LouiseLeciak/Module-elec-LilyPad/firmware/src/app/game.c

#include "app/game.h"

#include "app/menu.h"
#include "display/GC9A01.h"
#include "display/ili9488.h"
#include "display/screen_text.h"
#include "input/keypad.h"
#include "storage/fatfs.h"
#include "storage/sd_streaming.h"
#include "system/globals.h"
#include "system/power_save.h"
#include "system/uart.h"
#include "utils/utils.h"

uint8_t game_choice = 0;
game_state_t game_state = GAME_MENU;
char game_target;
// the different choices you have
char game_answers[GAME_CHOICES];
uint8_t game_answer = 0;  // player answer
uint32_t random_state = 0;

static const char game_characters[] = "0123456789ABCDEFGHIJKLMNOPQRSTUVWXYZ";

// manage keyboard in game mdd
void game()
{
  int key = keypad_read();

  if (key >= 0)
  {
    if (inac == 1)
    {
      power_save_activity();
      return;
    }
    else
      power_save_activity();
    uint8_t row = key / COLS_NB;
    uint8_t col = key % COLS_NB;
    char c = keymap[row][col];

    if (c == HOME)
    {
      show_menu();
    }

    _delay_ms(20);

    while (keypad_read() >= 0)
    {
      ;
    }
  }
}

// display teh game menu
void show_game(void)
{
  ili9488_fill_screen(GC9A01A_COLOR_OLIVE);
  if (language == LANG_FR)
  {
    draw_string(125, 20, "JEU", GC9A01A_COLOR_GREEN, GC9A01A_COLOR_OLIVE, 4, 2);

    draw_string(10, 120, "> ", GC9A01A_COLOR_GREEN, GC9A01A_COLOR_OLIVE, 4, 2);

    draw_string(70, 120, "Lettre", GC9A01A_COLOR_GREEN, GC9A01A_COLOR_OLIVE, 4,
                2);

    draw_string(70, 220, "Signe", GC9A01A_COLOR_GREEN, GC9A01A_COLOR_OLIVE, 4,
                2);
  }
  else if (language == LANG_EN)
  {
    draw_string(125, 20, "GAME", GC9A01A_COLOR_GREEN, GC9A01A_COLOR_OLIVE, 4,
                2);

    draw_string(10, 120, "> ", GC9A01A_COLOR_GREEN, GC9A01A_COLOR_OLIVE, 4, 2);

    draw_string(70, 120, "Letter game", GC9A01A_COLOR_GREEN,
                GC9A01A_COLOR_OLIVE, 4, 2);

    draw_string(70, 220, "Sign game", GC9A01A_COLOR_GREEN, GC9A01A_COLOR_OLIVE,
                4, 2);
  }
  game_choice = 0;
  game_state = GAME_MENU;
  app_state = JEU;
}

// to print the cursor of the game menu
// similar of the main menu one
void update_game_cursor(uint8_t old_choice)
{
  power_save_activity();

  if (old_choice == 0)
  {
    draw_string(10, 120, "  ", GC9A01A_COLOR_GREEN, GC9A01A_COLOR_OLIVE, 4, 2);
  }
  else
  {
    draw_string(10, 220, "  ", GC9A01A_COLOR_GREEN, GC9A01A_COLOR_OLIVE, 4, 2);
  }

  if (game_choice == 0)
  {
    draw_string(10, 120, "> ", GC9A01A_COLOR_GREEN, GC9A01A_COLOR_OLIVE, 4, 2);
  }
  else
  {
    draw_string(10, 220, "> ", GC9A01A_COLOR_GREEN, GC9A01A_COLOR_OLIVE, 4, 2);
  }
}

void update_game_answer_cursor(uint8_t old_choice)
{
  if (game_state == GAME_FIND_LETTER)
    return;
  uint16_t old_y;
  uint16_t new_y;

  old_y = 150 + old_choice * 70;
  new_y = 150 + game_answer * 70;

  // delete old cursos
  draw_string(10, old_y, " ", GC9A01A_COLOR_GREEN, GC9A01A_COLOR_OLIVE, 4, 2);

  // draw new cursor
  draw_string(10, new_y, ">", GC9A01A_COLOR_GREEN, GC9A01A_COLOR_OLIVE, 4, 2);
}

void display_game_letter_image(void)
{
  char letter[2];
  char file_name[16];

  letter[0] = game_target;
  letter[1] = '\0';

  file_name[0] = '\0';

  ft_strcat(file_name, letter);

  if (language == LANG_FR)
  {
    ft_strcat(file_name, "_GLSF");
  }
  else
  {
    ft_strcat(file_name, "_GBSL");
  }

  ft_strcat(file_name, "  BMP");

  for (uint8_t i = 0; i < IMG_LUT_MAX_SIZE && image_lut[i].address != 0; i++)
  {
    if (!ft_strncmp(file_name, image_lut[i].name, FILE_NAME_SIZE))
    {
      sd_stream_bmp_to_screen(cluster_to_lba(image_lut[i].address));
    }
  }
}

void display_find_letter(void)
{
  ili9488_fill_screen(GC9A01A_COLOR_OLIVE);

  if (language == LANG_FR)
  {
    draw_string(120, 20, "JEU", GC9A01A_COLOR_GREEN, GC9A01A_COLOR_OLIVE, 4, 2);

    draw_string(20, 150, "Clique pour voir", GC9A01A_COLOR_GREEN,
                GC9A01A_COLOR_OLIVE, 3, 2);

    draw_string(80, 190, "ton signe", GC9A01A_COLOR_GREEN, GC9A01A_COLOR_OLIVE,
                3, 2);
  }
  else
  {
    draw_string(120, 20, "GAME", GC9A01A_COLOR_GREEN, GC9A01A_COLOR_OLIVE, 4,
                2);

    draw_string(50, 150, "Click to see", GC9A01A_COLOR_GREEN,
                GC9A01A_COLOR_OLIVE, 3, 2);

    draw_string(80, 190, "your sign", GC9A01A_COLOR_GREEN, GC9A01A_COLOR_OLIVE,
                3, 2);
  }
}

void display_game_letter(void)
{
  char letter[2];
  char file_name[16] = {0};

  letter[0] = game_target;
  letter[1] = '\0';

  ft_strcat(file_name, letter);

  if (language == LANG_FR)
  {
    ft_strcat(file_name, "_GLSF");
  }
  else
  {
    ft_strcat(file_name, "_GBSL");
  }

  ft_strcat(file_name, "  BMP");

  for (uint8_t i = 0; i < IMG_LUT_MAX_SIZE && image_lut[i].address != 0; i++)
  {
    if (!ft_strncmp(file_name, image_lut[i].name, FILE_NAME_SIZE))
    {
      sd_stream_bmp_to_screen(cluster_to_lba(image_lut[i].address));
    }
  }
}

void random_update(void)
{
  random_state++;
  if (random_state % 10000 == 0 && inac == 0)
  {
    blink_front();
  }
}

// https://stackoverflow.com/questions/32225896/pseudo-random-function-in-c
//  this helped me
uint32_t simple_random(void)
{
  random_state = random_state * 1103515245UL + 12345UL;

  return random_state;
}
///////////////////////////////////////////////////////////////////
//////////////////////////  GAME 1  ///////////////////////////////
///////////////////////////////////////////////////////////////////
void start_find_letter(void)
{
  uint8_t correct_position;
  uint8_t target_position;
  uint8_t first_position;   // position of the first bad answer
  uint8_t second_position;  // pos of the second one

  game_state = GAME_FIND_LETTER;

  // choose the letter to find
  target_position =
      simple_random() % GAME_CHAR_COUNT;  // % bcs we have on 36 choices

  game_target = game_characters[target_position];

  // where the good answer will be
  correct_position = simple_random() % GAME_CHOICES;

  game_answers[correct_position] = game_target;

  // where is the first bad asnwer
  first_position = simple_random() % GAME_CHAR_COUNT;

  if (first_position == target_position)
  {
    first_position++;

    if (first_position >= GAME_CHAR_COUNT)
      first_position = 0;
  }

  // where is the second bad answer
  second_position = simple_random() % GAME_CHAR_COUNT;

  // check if similar of the good answer
  if (second_position == target_position)
  {
    second_position++;

    if (second_position >= GAME_CHAR_COUNT)
      second_position = 0;
  }

  // checking if similar of the other bad answer
  if (second_position == first_position)
  {
    second_position++;

    if (second_position >= GAME_CHAR_COUNT)
      second_position = 0;
  }

  // positions
  if (correct_position == 0)
  {
    game_answers[1] = game_characters[first_position];
    game_answers[2] = game_characters[second_position];
  }
  else if (correct_position == 1)
  {
    game_answers[0] = game_characters[first_position];
    game_answers[2] = game_characters[second_position];
  }
  else
  {
    game_answers[0] = game_characters[first_position];
    game_answers[1] = game_characters[second_position];
  }

  game_answer = 0;  // set the player choice at 0

#ifdef DEBUG
  uart_printstr("[GAME] Find Letter | target=");
  uart_tx(game_target);
  uart_printstr(" | choices=");
  uart_tx(game_answers[0]);
  uart_tx(' ');
  uart_tx(game_answers[1]);
  uart_tx(' ');
  uart_tx(game_answers[2]);
  uart_printstr("\r\n");
#endif

  display_find_letter();
}

///////////////////////////////////////////////////////////////////
//////////////////////////  GAME 2  ///////////////////////////////
///////////////////////////////////////////////////////////////////

void display_find_sign(void)
{
  char sign[2];

  sign[0] = game_target;
  sign[1] = '\0';

  ili9488_fill_screen(GC9A01A_COLOR_OLIVE);

  if (language == LANG_FR)
  {
    draw_string(120, 30, "JEU", GC9A01A_COLOR_GREEN, GC9A01A_COLOR_OLIVE, 4, 2);

    draw_string(20, 100, "Voici ta lettre :", GC9A01A_COLOR_GREEN,
                GC9A01A_COLOR_OLIVE, 3, 2);

    draw_string(140, 170, sign, GC9A01A_COLOR_WHITE, GC9A01A_COLOR_OLIVE, 12,
                2);

    draw_string(70, 280, "Clic pour voir", GC9A01A_COLOR_GREEN,
                GC9A01A_COLOR_OLIVE, 2, 2);

    draw_string(100, 310, "tes choix", GC9A01A_COLOR_GREEN, GC9A01A_COLOR_OLIVE,
                2, 2);
  }
  else if (language == LANG_EN)
  {
    draw_string(120, 30, "GAME", GC9A01A_COLOR_GREEN, GC9A01A_COLOR_OLIVE, 4,
                2);

    draw_string(20, 100, "Here's your letter :", GC9A01A_COLOR_GREEN,
                GC9A01A_COLOR_OLIVE, 3, 2);

    draw_string(140, 170, sign, GC9A01A_COLOR_WHITE, GC9A01A_COLOR_OLIVE, 12,
                2);

    draw_string(100, 280, "Click to see", GC9A01A_COLOR_GREEN,
                GC9A01A_COLOR_OLIVE, 2, 2);

    draw_string(100, 310, "your choices", GC9A01A_COLOR_GREEN,
                GC9A01A_COLOR_OLIVE, 2, 2);
  }
}

// you have to found which sign is the letter
void start_find_sign(void)
{
  uint8_t correct_position;
  uint8_t target_position;
  uint8_t first_position;
  uint8_t second_position;

  game_state = GAME_FIND_SIGN;

  // random letter to find
  target_position = simple_random() % GAME_CHAR_COUNT;
  game_target = game_characters[target_position];

  // place good answer
  correct_position = simple_random() % GAME_CHOICES;
  game_answers[correct_position] = game_target;

  // random first bad answer
  first_position = simple_random() % GAME_CHAR_COUNT;

  if (first_position == target_position)
  {
    first_position++;

    if (first_position >= GAME_CHAR_COUNT)
      first_position = 0;
  }

  // random second bad answer
  second_position = simple_random() % GAME_CHAR_COUNT;

  if (second_position == target_position)
  {
    second_position++;

    if (second_position >= GAME_CHAR_COUNT)
      second_position = 0;
  }

  if (second_position == first_position)
  {
    second_position++;

    if (second_position >= GAME_CHAR_COUNT)
      second_position = 0;
  }

  // place bad answer
  if (correct_position == 0)
  {
    game_answers[1] = game_characters[first_position];
    game_answers[2] = game_characters[second_position];
  }
  else if (correct_position == 1)
  {
    game_answers[0] = game_characters[first_position];
    game_answers[2] = game_characters[second_position];
  }
  else
  {
    game_answers[0] = game_characters[first_position];
    game_answers[1] = game_characters[second_position];
  }

  game_answer = 0;

#ifdef DEBUG
  uart_printstr("[GAME] Find Sign | target=");
  uart_tx(game_target);
  uart_printstr(" | choices=");
  uart_tx(game_answers[0]);
  uart_tx(' ');
  uart_tx(game_answers[1]);
  uart_tx(' ');
  uart_tx(game_answers[2]);
  uart_printstr("\r\n");
#endif

  display_find_sign();
}

//! INSERT IMAGE HERE
void display_sign_choice(uint8_t choice)
{
  char letter[2];
  char file_name[16] = {0};
  char number[2];

  // lettre pour image
  letter[0] = game_answers[choice];
  letter[1] = '\0';

  // numero de l;image
  number[0] = choice + '1';
  number[1] = '\0';

  ////////////////////////////////
  //// FILE NAME CONSTRUCTION ////
  ////////////////////////////////

  ft_strcat(file_name, letter);

  if (language == LANG_FR)
  {
    ft_strcat(file_name, "_GLSF");
  }
  else
  {
    ft_strcat(file_name, "_GBSL");
  }

  ft_strcat(file_name, "  BMP");

  // clean screen
  ili9488_fill_screen(GC9A01A_COLOR_OLIVE);

  // title
  if (language == LANG_FR)
  {
    draw_string(100, 30, "JEU", GC9A01A_COLOR_GREEN, GC9A01A_COLOR_OLIVE, 4, 2);
  }
  else
  {
    draw_string(100, 30, "GAME", GC9A01A_COLOR_GREEN, GC9A01A_COLOR_OLIVE, 4,
                2);
  }

  // img nb
  draw_string(100, 100, number, GC9A01A_COLOR_WHITE, GC9A01A_COLOR_OLIVE, 4, 2);

  draw_string(150, 100, ".", GC9A01A_COLOR_WHITE, GC9A01A_COLOR_OLIVE, 4, 2);

  // get img in sd
  for (uint8_t i = 0; i < IMG_LUT_MAX_SIZE && image_lut[i].address != 0; i++)
  {
    if (!ft_strncmp(file_name, image_lut[i].name, FILE_NAME_SIZE))
    {
      sd_stream_bmp_to_screen(cluster_to_lba(image_lut[i].address));

      break;
    }
  }
}

void display_letter_answers(void)
{
  char answer_text[2];

  ili9488_fill_screen(GC9A01A_COLOR_OLIVE);

  if (language == LANG_FR)
  {
    draw_string(20, 20, "JEU", GC9A01A_COLOR_GREEN, GC9A01A_COLOR_OLIVE, 4, 2);

    draw_string(20, 80, "Choisis :", GC9A01A_COLOR_GREEN, GC9A01A_COLOR_OLIVE,
                3, 2);
  }
  else
  {
    draw_string(20, 20, "GAME", GC9A01A_COLOR_GREEN, GC9A01A_COLOR_OLIVE, 4, 2);

    draw_string(20, 80, "Choose:", GC9A01A_COLOR_GREEN, GC9A01A_COLOR_OLIVE, 3,
                2);
  }

  answer_text[0] = game_answers[0];
  answer_text[1] = '\0';

  draw_string(10, 150, "> ", GC9A01A_COLOR_GREEN, GC9A01A_COLOR_OLIVE, 4, 2);

  draw_string(70, 150, answer_text, GC9A01A_COLOR_GREEN, GC9A01A_COLOR_OLIVE, 4,
              2);

  answer_text[0] = game_answers[1];

  draw_string(70, 220, answer_text, GC9A01A_COLOR_GREEN, GC9A01A_COLOR_OLIVE, 4,
              2);

  answer_text[0] = game_answers[2];

  draw_string(70, 290, answer_text, GC9A01A_COLOR_GREEN, GC9A01A_COLOR_OLIVE, 4,
              2);
}

/////////////////////////////////////////////
////////////////// YES NO////////////////////
/////////////////////////////////////////////

void display_game_yes(void)
{
  power_save_activity();
  win();
  ili9488_fill_screen(GC9A01A_COLOR_GREEN);

  draw_string(110, 170, "O", GC9A01A_COLOR_WHITE, GC9A01A_COLOR_GREEN, 20, 2);
}

void display_game_no(void)
{
  power_save_activity();
  loose();
  ili9488_fill_screen(GC9A01A_COLOR_RED);

  draw_string(110, 170, "X", GC9A01A_COLOR_WHITE, GC9A01A_COLOR_RED, 20, 2);
}
