LouiseLeciak/Module-elec-LilyPad/firmware/src/display/small_font.c

/* ************************************************************************** */
/*                                                                            */
/*                                                        :::      ::::::::   */
/*   small_font.c                                       :+:      :+:    :+:   */
/*                                                    +:+ +:+         +:+     */
/*   By: nige42 <nige42@student.42.fr>              +#+  +:+       +#+        */
/*                                                +#+#+#+#+#+   +#+           */
/*   Created: 2026/06/08 15:50:20 by nige42            #+#    #+#             */
/*   Updated: 2026/09/15 09:23:41 by nige42           ###   ########.fr       */
/*                                                                            */
/* ************************************************************************** */

#include "display/small_font.h"

#include <avr/io.h>
#include <avr/pgmspace.h>

// ─── 5x7 Font ────────────────────────────────────────────────────────────────
// Flat array covering ASCII 32-126.
// Each char = 5 bytes (one per column).
// Bits 0-6 of each byte = rows top-to-bottom.
// Unused chars are zero (blank).

// const uint8_t font5x7[95][5] = {
// { 0x00, 0x00, 0x00, 0x00, 0x00 },  // 32  ' '
// // { 0xFF, 0xFF, 0xFF, 0xFF, 0xFF },  // 32  ' '
// { 0x00, 0x00, 0x5F, 0x00, 0x00 },  // 33  '!'
// { 0x00, 0x07, 0x00, 0x07, 0x00 },  // 34  '"'
// { 0x14, 0x7F, 0x14, 0x7F, 0x14 },  // 35  '#'
// { 0x12, 0x2A, 0x7F, 0x2A, 0x24 },  // 36  '$'
// { 0x62, 0x64, 0x08, 0x13, 0x23 },  // 37  '%'
// { 0x50, 0x22, 0x55, 0x49, 0x36 },  // 38  '&'
// { 0x00, 0x00, 0x03, 0x05, 0x00 },  // 39  '''
// { 0x00, 0x41, 0x22, 0x1C, 0x00 },  // 40  '('
// { 0x00, 0x1C, 0x22, 0x41, 0x00 },  // 41  ')'
// { 0x14, 0x08, 0x3E, 0x08, 0x14 },  // 42  '*'
// { 0x08, 0x08, 0x3E, 0x08, 0x08 },  // 43  '+'
// { 0x00, 0x00, 0x30, 0x50, 0x00 },  // 44  ','
// { 0x08, 0x08, 0x08, 0x08, 0x08 },  // 45  '-'
// { 0x00, 0x00, 0x60, 0x60, 0x00 },  // 46  '.'
// { 0x02, 0x04, 0x08, 0x10, 0x20 },  // 47  '/'  // OK
// { 0x3E, 0x45, 0x49, 0x51, 0x3E },  // 48  '0' // 16
// { 0x00, 0x42, 0x7F, 0x40, 0x00 },  // 49  '1'
// // { 0x00, 0x40, 0x7F, 0x42, 0x00 },  // 49  '1'
// { 0x62, 0x61, 0x51, 0x49, 0x46 },  // 50 '2'
// // { 0x46, 0x49, 0x51, 0x61, 0x62 },  // 50 '2'
// { 0x31, 0x4B, 0x45, 0x41, 0x21 },  // 51  '3'
// { 0x10, 0x7F, 0x12, 0x14, 0x18 },  // 52  '4'
// { 0x39, 0x45, 0x45, 0x45, 0x27 },  // 53  '5'
// { 0x30, 0x49, 0x49, 0x4A, 0x3C },  // 54  '6'
// { 0x03, 0x05, 0x09, 0x71, 0x01 },  // 55  '7'
// { 0x36, 0x49, 0x49, 0x49, 0x36 },  // 56  '8'
// { 0x1E, 0x29, 0x49, 0x49, 0x06 },  // 57  '9'
// { 0x00, 0x00, 0x36, 0x36, 0x00 },  // 58  ':'
// { 0x00, 0x00, 0x36, 0x56, 0x00 },  // 59  ';'
// { 0x00, 0x41, 0x22, 0x14, 0x08 },  // 60  '<'
// { 0x14, 0x14, 0x14, 0x14, 0x14 },  // 61  '=' // 29
// { 0x08, 0x14, 0x22, 0x41, 0x00 },  // 62  '>' // OK
// { 0x06, 0x09, 0x51, 0x01, 0x02 },  // 63  '?'
// { 0x3E, 0x41, 0x79, 0x49, 0x32 },  // 64  '@'
// { 0x7E, 0x11, 0x11, 0x11, 0x7E },  // 65  'A'
// { 0x36, 0x49, 0x49, 0x49, 0x7F },  // 66  'B'
// { 0x22, 0x41, 0x41, 0x41, 0x3E },  // 67  'C'
// { 0x1C, 0x22, 0x41, 0x41, 0x7F },  // 68  'D'
// { 0x7F, 0x49, 0x49, 0x49, 0x41 },  // 69  'E'
// //{ 0x41, 0x49, 0x49, 0x49, 0x7F },  // 69  'E'
// { 0x01, 0x09, 0x09, 0x09, 0x7F },  // 70  'F'
// { 0x7A, 0x49, 0x49, 0x41, 0x3E },  // 71  'G'
// { 0x7F, 0x08, 0x08, 0x08, 0x7F },  // 72  'H'
// { 0x00, 0x41, 0x7F, 0x41, 0x00 },  // 73  'I'
// { 0x01, 0x3F, 0x41, 0x40, 0x20 },  // 74  'J'
// { 0x41, 0x22, 0x14, 0x08, 0x7F },  // 75  'K'
// { 0x40, 0x40, 0x40, 0x40, 0x7F },  // 76  'L'
// { 0x7F, 0x02, 0x0C, 0x02, 0x7F },  // 77  'M'
// { 0x7F, 0x10, 0x08, 0x04, 0x7F },  // 78  'N'
// { 0x3E, 0x41, 0x41, 0x41, 0x3E },  // 79  'O'
// { 0x06, 0x09, 0x09, 0x09, 0x7F },  // 80  'P'
// { 0x5E, 0x21, 0x51, 0x41, 0x3E },  // 81  'Q'
// { 0x46, 0x29, 0x19, 0x09, 0x7F },  // 82  'R'
// { 0x31, 0x49, 0x49, 0x49, 0x46 },  // 83  'S'
// { 0x01, 0x01, 0x7F, 0x01, 0x01 },  // 84  'T'
// { 0x3F, 0x40, 0x40, 0x40, 0x3F },  // 85  'U'
// { 0x1F, 0x20, 0x40, 0x20, 0x1F },  // 86  'V'
// { 0x3F, 0x40, 0x38, 0x40, 0x3F },  // 87  'W'
// { 0x63, 0x14, 0x08, 0x14, 0x63 },  // 88  'X'
// { 0x07, 0x08, 0x70, 0x08, 0x07 },  // 89  'Y'
// { 0x43, 0x45, 0x49, 0x51, 0x61 },  // 90  'Z'
// { 0x00, 0x41, 0x41, 0x7F, 0x00 },  // 91  '['
// { 0x20, 0x10, 0x08, 0x04, 0x02 },  // 92  '\'
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
    {0x1F, 0x20, 0x40, 0x20, 0x1F},  // 86  'V'
    {0x3F, 0x40, 0x38, 0x40, 0x3F},  // 87  'W'
    {0x63, 0x14, 0x08, 0x14, 0x63},  // 88  'X'
    {0x07, 0x08, 0x70, 0x08, 0x07},  // 89  'Y'
    {0x61, 0x51, 0x49, 0x45, 0x43},  // 90  'Z'
    {0x00, 0x7F, 0x41, 0x41, 0x00},  // 91  '['
    {0x02, 0x04, 0x08, 0x10, 0x20},  // 92  '\'
    {0x00, 0x41, 0x41, 0x7F, 0x00},  // 93  ']'
    {0x04, 0x02, 0x01, 0x02, 0x04},  // 94  '^'
    {0x40, 0x40, 0x40, 0x40, 0x40},  // 95  '_'
    {0x00, 0x01, 0x02, 0x04, 0x00},  // 96  '`'
    {0x20, 0x54, 0x54, 0x54, 0x78},  // 97  'a'
    {0x7F, 0x48, 0x44, 0x44, 0x38},  // 98  'b'
    {0x38, 0x44, 0x44, 0x44, 0x20},  // 99  'c'
    {0x38, 0x44, 0x44, 0x48, 0x7F},  // 100 'd'
    {0x38, 0x54, 0x54, 0x54, 0x18},  // 101 'e'
    {0x08, 0x7E, 0x09, 0x01, 0x02},  // 102 'f'
    {0x0C, 0x52, 0x52, 0x52, 0x3E},  // 103 'g'
    {0x7F, 0x08, 0x04, 0x04, 0x78},  // 104 'h'
    {0x00, 0x44, 0x7D, 0x40, 0x00},  // 105 'i'
    {0x20, 0x40, 0x44, 0x3D, 0x00},  // 106 'j'
    {0x7F, 0x10, 0x28, 0x44, 0x00},  // 107 'k'
    {0x00, 0x41, 0x7F, 0x40, 0x00},  // 108 'l'
    {0x7C, 0x04, 0x18, 0x04, 0x78},  // 109 'm'
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
};
