LouiseLeciak/Module-elec-LilyPad/firmware/src/app/menu.c

#include "display/GC9A01.h"
#include "display/ili9488.h"
#include "display/screen_text.h"
#include "storage/fatfs.h"
#include "storage/sd_streaming.h"
#include "system/globals.h"
#include "system/uart.h"
#include "utils/keyboard_utils.h"
#include "utils/utils.h"

// to display the different choicies
void show_menu(void)
{
  ili9488_fill_screen(GC9A01A_COLOR_OLIVE);
  if (language == LANG_FR)
  {
    draw_string(100, 20, "Menu", GC9A01A_COLOR_GREEN, GC9A01A_COLOR_OLIVE, 5,
                2);

    if (menu_choice == 0)
    {
      draw_string(10, 120, "> Traduction", GC9A01A_COLOR_GREEN,
                  GC9A01A_COLOR_OLIVE, 4, 2);
    }
    else
    {
      draw_string(10, 120, "  Traduction", GC9A01A_COLOR_GREEN,
                  GC9A01A_COLOR_OLIVE, 4, 2);
    }

    if (menu_choice == 1)
    {
      draw_string(10, 220, "> Alphabet", GC9A01A_COLOR_GREEN,
                  GC9A01A_COLOR_OLIVE, 4, 2);
    }
    else
    {
      draw_string(10, 220, "  Alphabet", GC9A01A_COLOR_GREEN,
                  GC9A01A_COLOR_OLIVE, 4, 2);
    }

    if (menu_choice == 2)
    {
      draw_string(10, 320, "> Jeu", GC9A01A_COLOR_GREEN, GC9A01A_COLOR_OLIVE, 4,
                  2);
    }
    else
    {
      draw_string(10, 320, "  Jeu", GC9A01A_COLOR_GREEN, GC9A01A_COLOR_OLIVE, 4,
                  2);
    }
  }
  else if (language == LANG_EN)
  {  // POUR ANGLAIS
    draw_string(100, 20, "Menu", GC9A01A_COLOR_GREEN, GC9A01A_COLOR_OLIVE, 5,
                2);

    if (menu_choice == 0)
    {
      draw_string(10, 120, "> Translation", GC9A01A_COLOR_GREEN,
                  GC9A01A_COLOR_OLIVE, 4, 2);
    }
    else
    {
      draw_string(10, 120, "  Translation", GC9A01A_COLOR_GREEN,
                  GC9A01A_COLOR_OLIVE, 4, 2);
    }

    if (menu_choice == 1)
    {
      draw_string(10, 220, "> Alphabet", GC9A01A_COLOR_GREEN,
                  GC9A01A_COLOR_OLIVE, 4, 2);
    }
    else
    {
      draw_string(10, 220, "  Alphabet", GC9A01A_COLOR_GREEN,
                  GC9A01A_COLOR_OLIVE, 4, 2);
    }

    if (menu_choice == 2)
    {
      draw_string(10, 320, "> Game", GC9A01A_COLOR_GREEN, GC9A01A_COLOR_OLIVE,
                  4, 2);
    }
    else
    {
      draw_string(10, 320, "  Game", GC9A01A_COLOR_GREEN, GC9A01A_COLOR_OLIVE,
                  4, 2);
    }
  }

  app_state = MENU;
}

void update_menu_cursor(uint8_t old_choice)
{
  // on enelve lancien curseur et on met un espace
  if (old_choice == 0)
  {
    draw_string(10, 120, "  ", GC9A01A_COLOR_GREEN, GC9A01A_COLOR_OLIVE, 4, 2);
  }
  else if (old_choice == 1)
  {
    draw_string(10, 220, "  ", GC9A01A_COLOR_GREEN, GC9A01A_COLOR_OLIVE, 4, 2);
  }
  else
  {
    draw_string(10, 320, "  ", GC9A01A_COLOR_GREEN, GC9A01A_COLOR_OLIVE, 4, 2);
  }

  // nouveau curseur
  if (menu_choice == 0)
  {
    draw_string(10, 120, "> ", GC9A01A_COLOR_GREEN, GC9A01A_COLOR_OLIVE, 4, 2);
  }
  else if (menu_choice == 1)
  {
    draw_string(10, 220, "> ", GC9A01A_COLOR_GREEN, GC9A01A_COLOR_OLIVE, 4, 2);
  }
  else
  {
    draw_string(10, 320, "> ", GC9A01A_COLOR_GREEN, GC9A01A_COLOR_OLIVE, 4, 2);
  }
}

void show_bonjour()
{
  uart_printstr("PRINT: BONJOUR IMAGE\n\r");
  char file_name[16] = {0};

  ft_strcat(file_name, "BONJOUR BMP");

  for (uint8_t i = 0; i < IMG_LUT_MAX_SIZE && image_lut[i].address != 0; i++)
  {
    if (!ft_strncmp(file_name, image_lut[i].name, FILE_NAME_SIZE))
    {
      sd_stream_bmp_to_screen(cluster_to_lba(image_lut[i].address));
      break;
    }
  }
}

void show_hello()
{
  uart_printstr("PRINT: HELLO IMAGE\n\r");
  char file_name[16] = {0};

  ft_strcat(file_name, "HELLO   BMP");

  for (uint8_t i = 0; i < IMG_LUT_MAX_SIZE && image_lut[i].address != 0; i++)
  {
    if (!ft_strncmp(file_name, image_lut[i].name, FILE_NAME_SIZE))
    {
      sd_stream_bmp_to_screen(cluster_to_lba(image_lut[i].address));
      break;
    }
  }
}
