LouiseLeciak/Module-elec-LilyPad/firmware/src/app/language.c

#include "app/language.h"

#include <avr/io.h>

#include "app/menu.h"
#include "display/GC9A01.h"
#include "pinout.h"
#include "system/globals.h"
#include "system/power_save.h"
#include "system/uart.h"

language_t language = LANG_FR;

// init the slide switch
// pc1 <-> pc2 ; pc2 <-> pc3
void language_switch_init(void)
{
  // pc1 et pc3 avec pull up
  // entree a 1
  DDRC &= ~(SDL_SW1 | SDL_SW3);
  PORTC |= SDL_SW1 | SDL_SW3;

  // pc2, different comme c;est le point commun
  // sortie a 0
  DDRC |= SDL_SW2;
  PORTC &= ~SDL_SW2;
}

// to know the language at the inti
void language_init(void)
{
  if (!(PINC & SDL_SW1))
    language = LANG_FR;
  else if (!(PINC & SDL_SW3))
    language = LANG_EN;
}

// change the language when moving the slide switch
void language_update(void)
{
  language_t new_language;
  // if on the left -> fr
  // pc1 = 0 car relie a pc2 qui est a 0
  if (!(PINC & SDL_SW1))
  {
    new_language = LANG_FR;
  }
  else if (!(PINC & SDL_SW3))  // right -> en
  {
    new_language = LANG_EN;
  }
  else
  {
    return;
  }

  if (new_language != language)
  {
    power_save_activity();

    language = new_language;
#ifdef DEBUG
    uart_printstr("[LANG] Switched to ");
    uart_printstr(language == LANG_FR ? "FR" : "EN");
    uart_printstr("\r\n");
#endif /* ifdef DEBUG */
    // go back to the menu when we switch language
    menu_choice = 0;
    if (language == LANG_FR)
      show_bonjour();
    else
      show_hello();
    _delay_ms(300);
    show_menu();
    return;
  }
}
