LouiseLeciak/Module-elec-LilyPad/firmware/src/system/power_save.c

#include "system/power_save.h"

#include "display/GC9A01.h"
#include "pinout.h"
#include "system/uart.h"

uint32_t inactivity_counter = 0;
uint8_t inac = 0;

// timer to know since when nothing is happening
void power_save_update(void)
{
  // 30000 ~= 23s
  if (inactivity_counter < 30000)
    inactivity_counter++;

  if (inactivity_counter >= 30000)
  {
    if (inac == 0)
#ifdef DEBUG
      uart_printstr("[PWR] Screen sleeping (inactivity timeout)\r\n");
#endif                         /* ifdef DEBUG */
    PORTH &= ~MAIN_SCREEN_BL;  // on eteint
    CS_LEFT_EYE_LOW();
    CS_RIGHT_EYE_LOW();
    GC9A01_eye_Lids_down();
    GC9A01_setAddrWindow_eyes(0, 0, 239, 219);
    GC9A01_draw_eye_Lids(FULLSCREEN, GC9A01A_COLOR_GREEN);
    CS_LEFT_EYE_HIGH();
    CS_RIGHT_EYE_HIGH();
    inac = 1;
  }
  return;
}

// ping if activity
void power_save_activity(void)
{
  inactivity_counter = 0;

  if (inac == 1)
  {
#ifdef DEBUG
    uart_printstr("[PWR] Screen waking up\r\n");
#endif /* ifdef DEBUG */
    PORTH |= MAIN_SCREEN_BL;
    eyes_action();  // pose un pb je crois, c;est pas toujours bine
    //   responsive, a tester
    inac = 0;
  }
}
