LouiseLeciak/Module-elec-LilyPad/firmware/src/storage/sd_streaming.c

#include "storage/sd_streaming.h"

#include "display/bmp.h"
#include "display/ili9488.h"
#include "pinout.h"
#include "storage/sd.h"
#include "system/spi.h"
#include "system/uart.h"
#include "utils/utils.h"

union Buffers
{
  uint8_t header[512];
  uint8_t img[512];
};

static union Buffers buffers = {0};

void sd_stream_bmp_to_screen(uint32_t start_sector)
{
  sd_read_single_block(start_sector >> 24, start_sector >> 16,
                       start_sector >> 8, start_sector, buffers.header);
  bmp_header header = {0};
  if (bmp_parse_header(buffers.header, &header) != 0)
  {
    uart_printstr("Error while printing image\r\n");
    return;  // ERROR
  }
  uint32_t abs_height = (header.height < 0 ? -header.height : header.height);
  window win = {{0, 0}, {header.width - 1, abs_height - 1}};

#ifdef DEBUG
  uart_printstr("Starting printing image\r\n");
#endif /* ifdef DEBUG */

  MAIN_SCREEN_CS_LOW();
  ili9488_set_window(win);
  ili9488_ramwr();
  MAIN_SCREEN_CS_HIGH();

  uint32_t pixel_sector = start_sector + (header.pixel_data_offset / 512);
  uint16_t buffer_idx = header.pixel_data_offset % 512;

  uint32_t byte_count = (uint32_t)abs_height * header.width * 3;
#ifdef DEBUG
  uart_printstr("byte_count= ");
  uart_printhex_32(byte_count);
  uart_printstr("\r\n");
#endif /* ifdef DEBUG */
  uint32_t bytes_processed = 0;

  uint8_t rgb[3];
  uint8_t rgb_idx = 0;

  while (bytes_processed < byte_count)
  {
    sd_read_single_block(pixel_sector >> 24, pixel_sector >> 16,
                         pixel_sector >> 8, pixel_sector, buffers.img);
    pixel_sector++;
    MAIN_SCREEN_CS_LOW();

    for (; buffer_idx < 512 && bytes_processed < byte_count; buffer_idx++)
    {
      rgb[rgb_idx++] = buffers.img[buffer_idx];

      if (rgb_idx == 3)
      {
        spi_txrx(rgb[2] & 0xFC);  // R
        spi_txrx(rgb[1] & 0xFC);  // G
        spi_txrx(rgb[0] & 0xFC);  // B
        rgb_idx = 0;
      }
      bytes_processed++;
    }

    MAIN_SCREEN_CS_HIGH();
    buffer_idx = 0;
  }
#ifdef DEBUG
  uart_printstr("Finished printing image\r\n");
#endif /* ifdef DEBUG */
}
